walterwhiteita/esp8266-mqtt-gate-controller/firmware/src/settings.h

#define BUTTON_DEBOUNCE_DELAY   20   // [ms]
#define STATE_TOPIC "/stat"
#define COMMAND_TOPIC "/cmnd"
#define AVAILABILITY_TOPIC "/availability"
#define FORCE_UPDATE_TIME 60000
#define CLICK_TIME 500
#define CORRECT_NUM_OF_LECTURES 50
#define DEFAULT_CLIENTID_PREFIX "CameWifi-"
#define AP_SSID "came_wifi"
#define AP_PASSWORD "came2024"
